blackjetrock/pico-rom-emulator/code/pico-rom-em/scope_traces/rl_ram_siz1.jpg

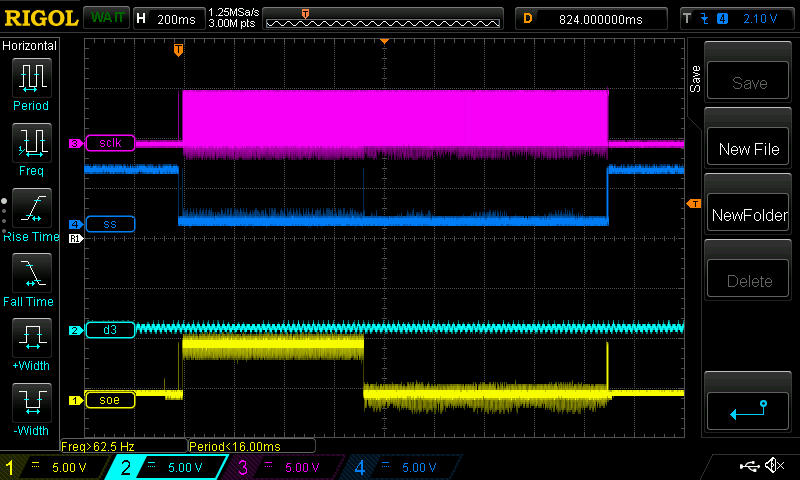
code/pico-rom-em/scope_traces/rl_ram_siz1.jpg
