blackjetrock/pico-rom-emulator/code/pico-rom-em/scope_traces/isr1.jpg

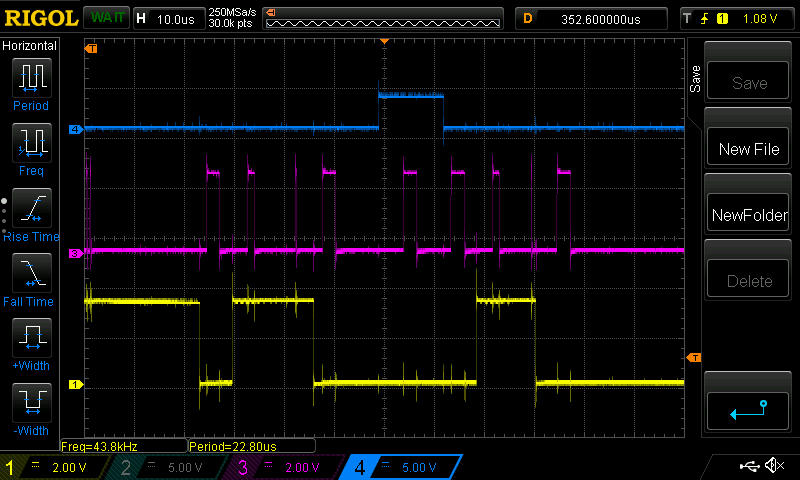
code/pico-rom-em/scope_traces/isr1.jpg
