blackjetrock/pico-rom-emulator/code/pico-rom-em/scope_traces/NewFile1.jpg

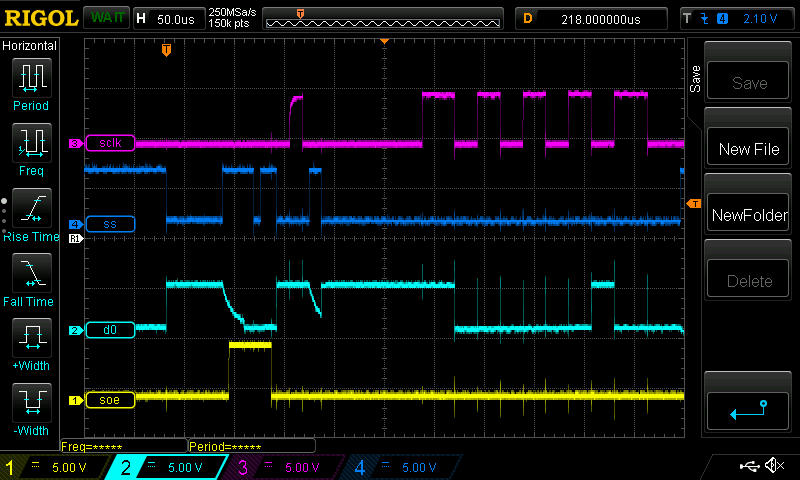
code/pico-rom-em/scope_traces/NewFile1.jpg
