blackjetrock/pico-rom-emulator/code/pico-rom-em/scope_traces/NewFile3.jpg

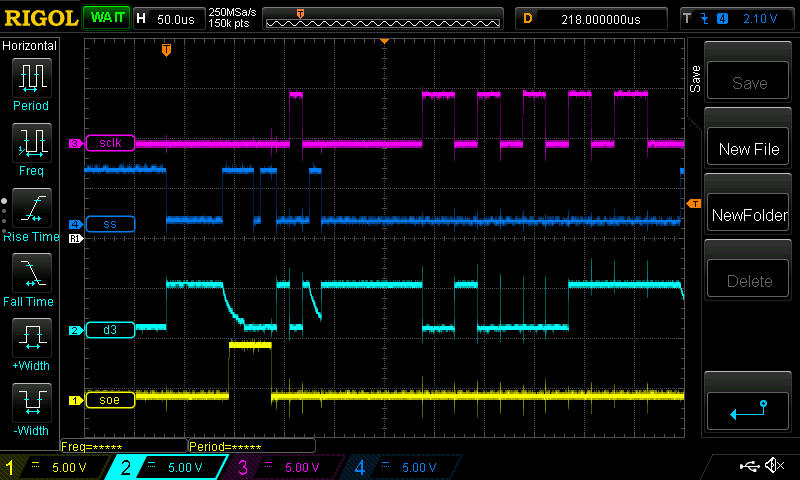
code/pico-rom-em/scope_traces/NewFile3.jpg
