blackjetrock/pico-rom-emulator/code/pico-rom-em/scope_traces/NewFile4.jpg

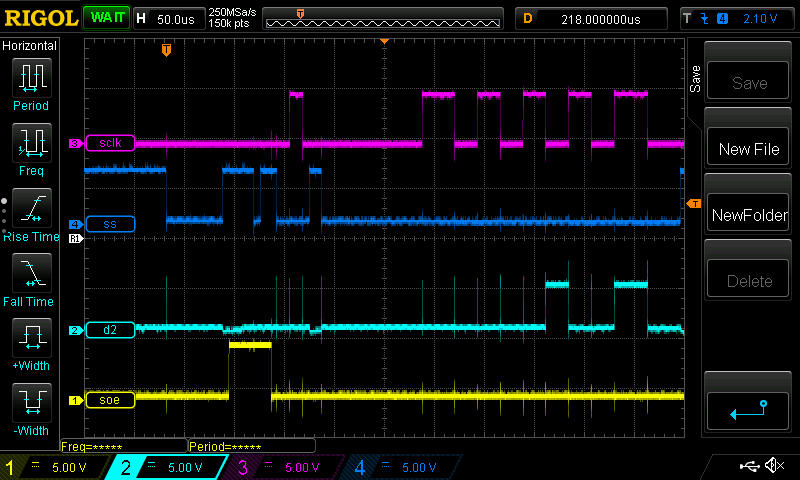
code/pico-rom-em/scope_traces/NewFile4.jpg
