blackjetrock/pico-rom-emulator/code/pico-rom-em/scope_traces/NewFile5.jpg

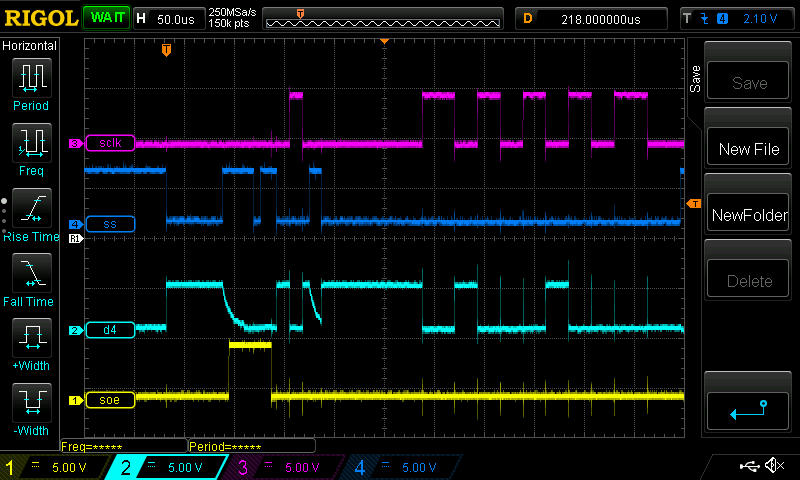
code/pico-rom-em/scope_traces/NewFile5.jpg
