blackjetrock/pico-rom-emulator/code/pico-rom-em/scope_traces/NewFile7.jpg

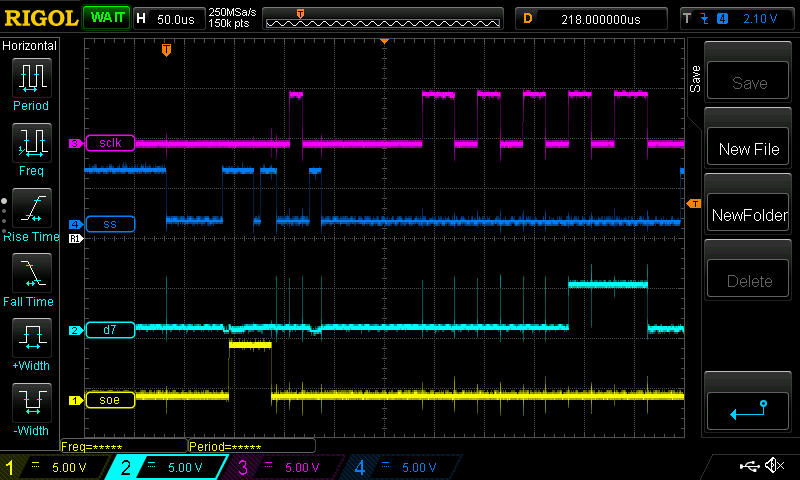
code/pico-rom-em/scope_traces/NewFile7.jpg
