blackjetrock/pico-rom-emulator/code/pico-rom-em/scope_traces/NewFile8.jpg

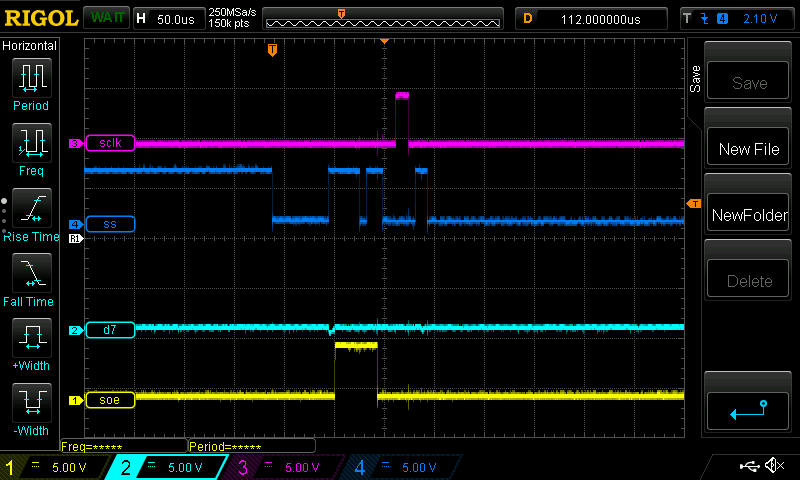
code/pico-rom-em/scope_traces/NewFile8.jpg
