blackjetrock/pico-rom-emulator/code/pico-rom-em/scope_traces/NewFile9.jpg

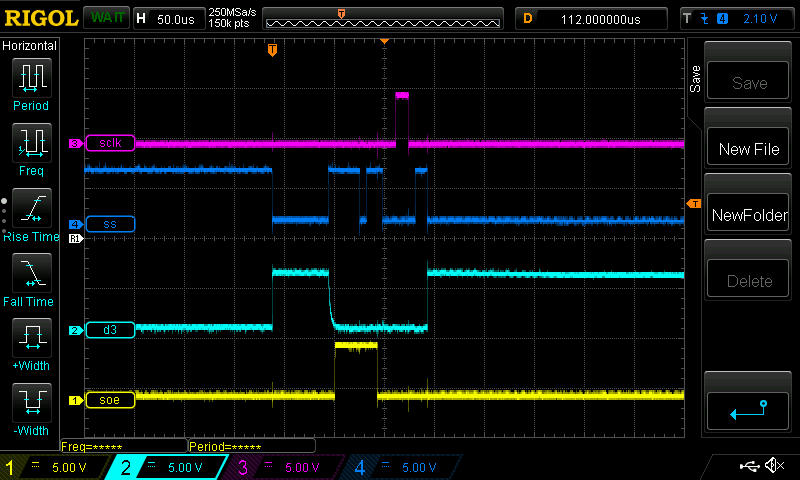
code/pico-rom-em/scope_traces/NewFile9.jpg
