blackjetrock/pico-rom-emulator/code/pico-rom-em/scope_traces/on1.jpg

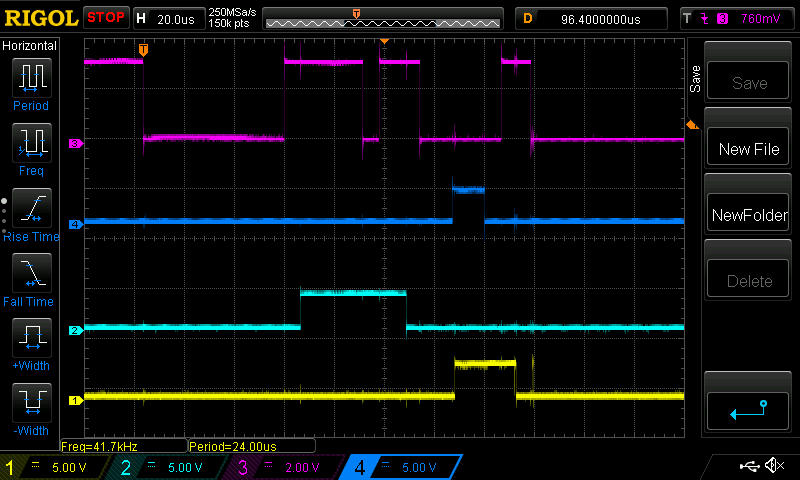
code/pico-rom-em/scope_traces/on1.jpg
