blackjetrock/pico-rom-emulator/code/pico-rom-em/scope_traces/on1b.jpg

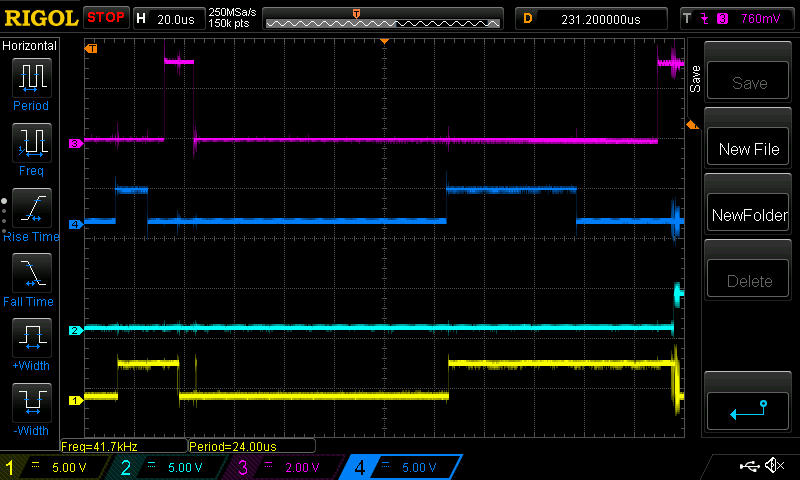
code/pico-rom-em/scope_traces/on1b.jpg
