blackjetrock/pico-rom-emulator/code/pico-rom-em/scope_traces/on2.jpg

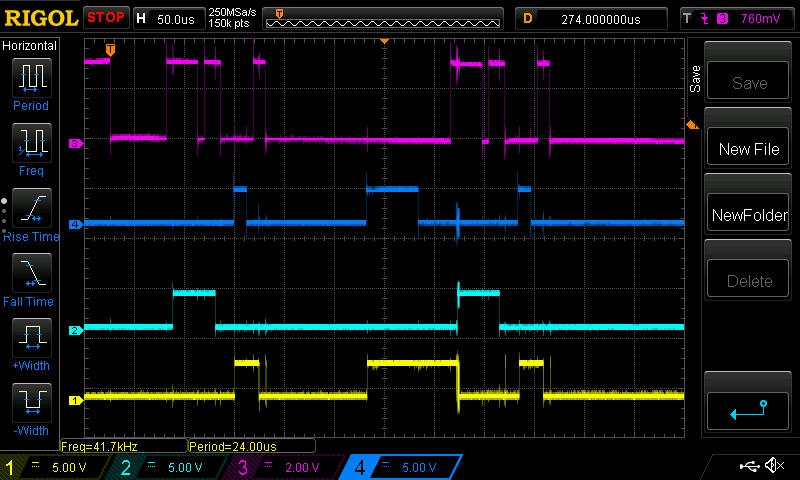
code/pico-rom-em/scope_traces/on2.jpg
