blackjetrock/pico-rom-emulator/code/pico-rom-em/scope_traces/RAMPAK1.jpg

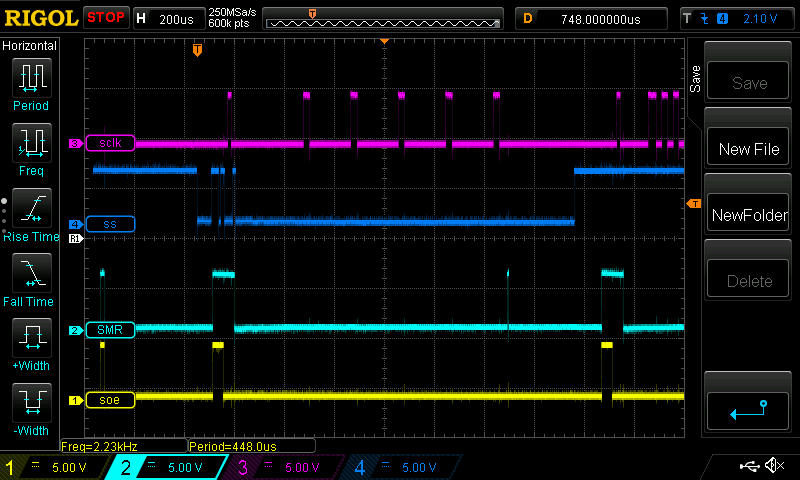
code/pico-rom-em/scope_traces/RAMPAK1.jpg
