blackjetrock/pico-rom-emulator/code/pico-rom-em/scope_traces/RAMPAK3.jpg

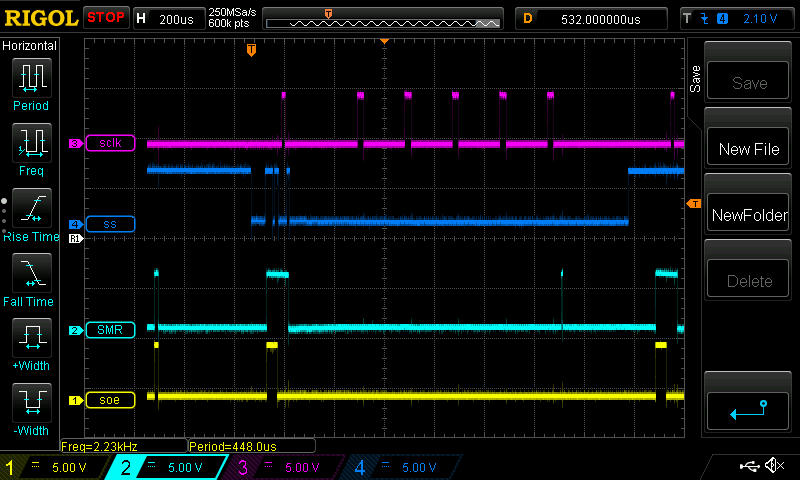
code/pico-rom-em/scope_traces/RAMPAK3.jpg
