blackjetrock/pico-rom-emulator/code/pico-rom-em/scope_traces/RDONLY1.jpg

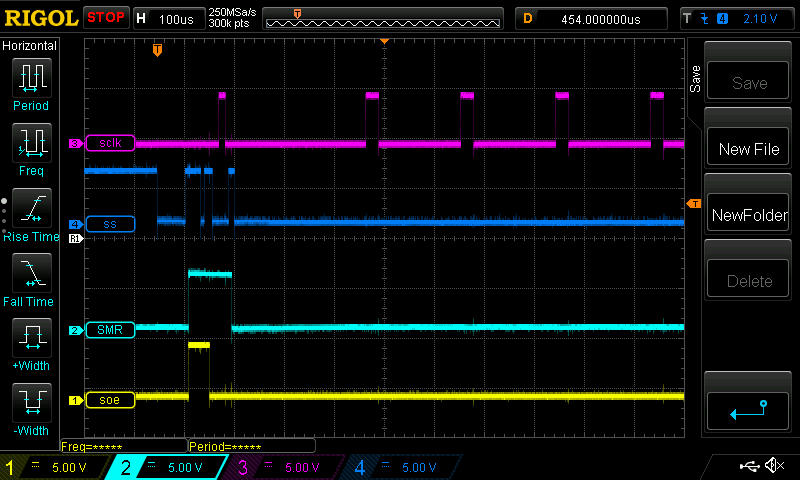
code/pico-rom-em/scope_traces/RDONLY1.jpg
