blackjetrock/pico-rom-emulator/code/pico-rom-em/scope_traces/rl_ep_pgm.jpg

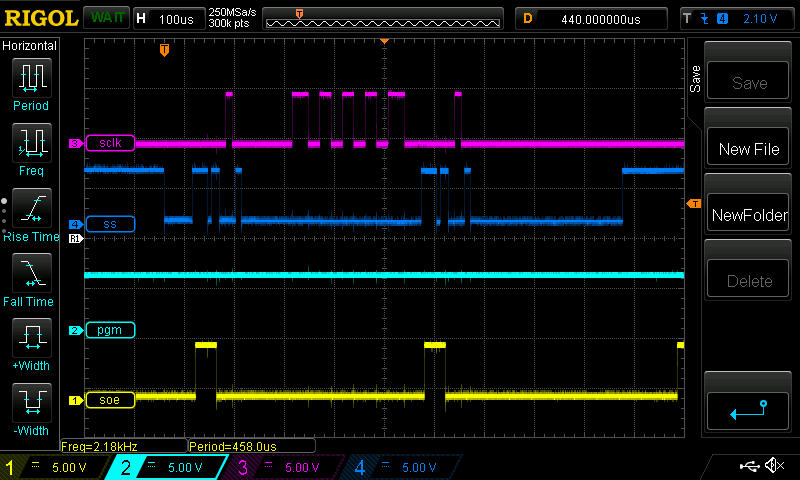
code/pico-rom-em/scope_traces/rl_ep_pgm.jpg
