blackjetrock/pico-rom-emulator/code/pico-rom-em/scope_traces/rl_epd1.jpg

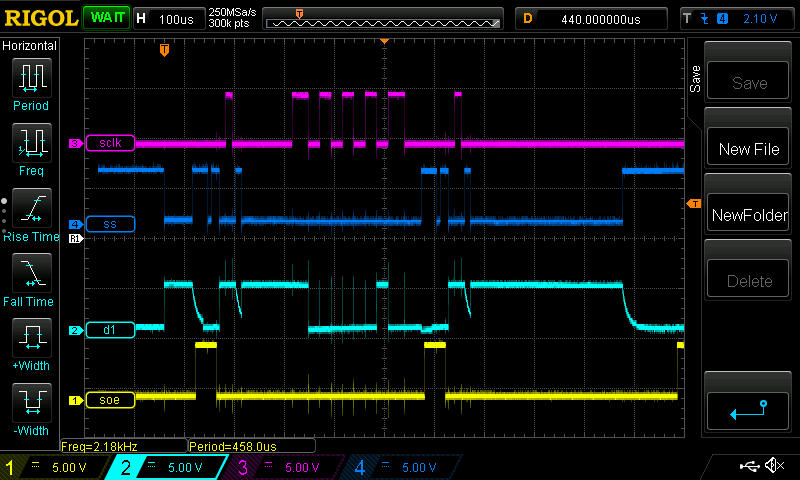
code/pico-rom-em/scope_traces/rl_epd1.jpg
