blackjetrock/pico-rom-emulator/code/pico-rom-em/scope_traces/rl_ra_smr.jpg

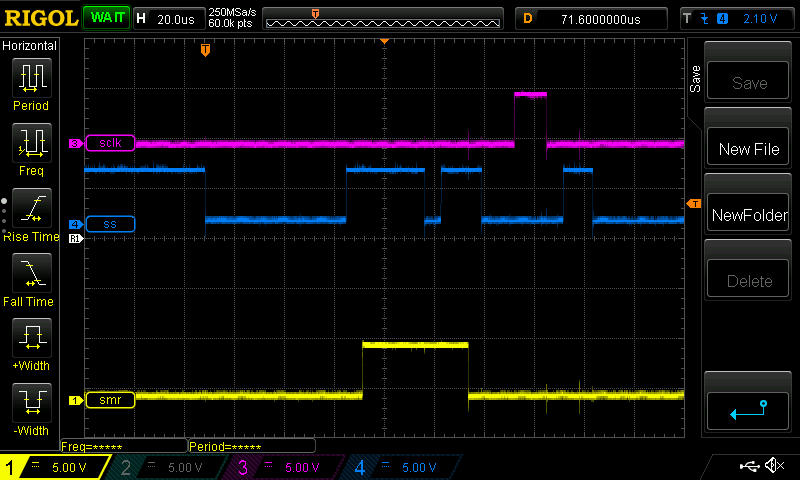
code/pico-rom-em/scope_traces/rl_ra_smr.jpg
