blackjetrock/pico-rom-emulator/code/pico-rom-em/scope_traces/rra1.jpg

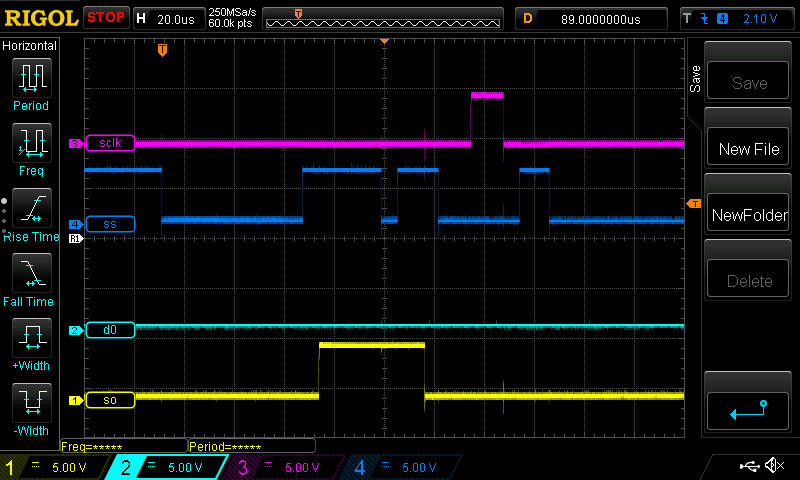
code/pico-rom-em/scope_traces/rra1.jpg
