blackjetrock/pico-rom-emulator/code/pico-rom-em/scope_traces/rra3.jpg

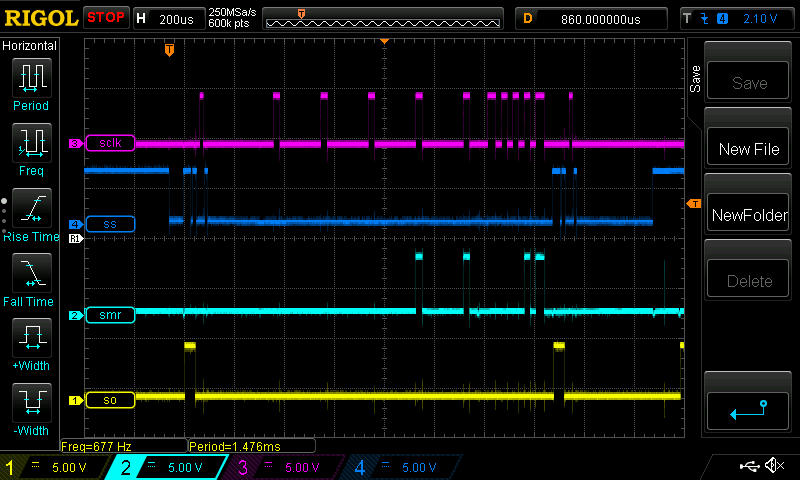
code/pico-rom-em/scope_traces/rra3.jpg
