blackjetrock/pico-rom-emulator/code/pico-rom-em/pico-rom-em.c

////////////////////////////////////////////////////////////////////////////////
//
// Pico ROM Emulator
//
////////////////////////////////////////////////////////////////////////////////


#include <ctype.h>
#include <stdio.h>
#include <string.h>
#include <stdlib.h>
#include "pico/stdlib.h"
//#include "hardware/i2c.h"
#include "hardware/pio.h"
#include "hardware/clocks.h"
#include "pico/multicore.h"

#include "f_util.h"

#include "ff.h"
#include "ff_stdio.h"
#include "hw_config.h"
#include "my_debug.h"
#include "rtc.h"
#include "sd_card.h"

// Use this if breakpoints don't work
#define DEBUG_STOP {volatile int x = 1; while(x) {} }

//-----------------------------------------------------------------------------
//
// ROM Emulator Flags

// OE pin used to switch data direction
// If 0 then DDIR_A15 used, under processor conrol

#define USE_OE_FOR_DATA_DIRECTION 1

// The address lines we are looking at

// Do we run emulation on second core?
#define EMULATE_ON_CORE1   1

#define ROM_SIZE  32*1024
#define ADDRESS_MASK (ROM_SIZE - 1)

// Map from memory space to ROM address space
#define MAP_ROM(X) (X & ADDRESS_MASK)

uint8_t rom_data[ROM_SIZE] =
  {
   // ASSEMBLER_EMBEDDED_CODE_START
0x72,0x40,0x14,0x71,0xe0,0x14,0x8e,0x00,0xff,0xbd,0xab,0x07,0x4f,0x97,0x01,0xbd,
0xd8,0x4b,0x96,0x14,0x2b,0x60,0xce,0x04,0x00,0xcc,0x55,0xaa,0xed,0x00,0xa3,0x00,
0x26,0x08,0x08,0x8c,0x7f,0xff,0x26,0xf1,0x20,0x54,0x08,0x8c,0x40,0x00,0x27,0x4e,
0x8c,0x60,0x00,0x27,0x49,0xbd,0xa5,0x7f,0x20,0x37,0x07,0xd6,0x08,0xfd,0x20,0x63,
0x0f,0xbd,0xab,0x38,0x8d,0x5f,0x7d,0x01,0x80,0x2b,0xfb,0xb6,0x01,0x81,0xa7,0x00,
0x08,0x5a,0x26,0xf2,0x3f,0x5b,0x7d,0x03,0x00,0xbd,0xa4,0xde,0xce,0x08,0x00,0xdf,
0x5c,0x24,0x08,0xdd,0x5c,0x18,0x93,0x5c,0xbd,0x81,0x05,0x7d,0x03,0xc0,0x71,0xbf,
0x14,0x7d,0x01,0xc0,0x20,0x8a,0xbe,0x20,0x67,0xfe,0x20,0x56,0x6e,0x00,0x72,0x80,
0x14,0xdf,0x5e,0x35,0xbd,0x81,0x16,0xbd,0xe8,0xb1,0x7d,0x03,0x80,0xbd,0x83,0xe3,
0x96,0x15,0x46,0x24,0x02,0x8d,0x62,0x7e,0xe4,0xa6,0xfc,0x20,0x63,0xd7,0x08,0x06,
0x8d,0x03,0x7e,0xab,0xdd,0xcc,0x40,0x40,0xbd,0xab,0x1e,0xce,0x22,0x88,0x39,0xbd,
0x81,0x9a,0xde,0x5c,0x3c,0x7b,0x02,0x15,0x27,0x17,0xcc,0x08,0x00,0x8d,0x46,0xbd,
0x81,0xaa,0x38,0xbd,0x81,0xb9,0x8d,0xd2,0xde,0x5c,0x8c,0x08,0x00,0x27,0x2d,0x20,
0x07,0x38,0x09,0xbd,0x81,0xad,0x8d,0xc2,0xbd,0xab,0xd7,0x7c,0x23,0x4a,0xfe,0x20,
0xcd,0x8c,0x00,0x0f,0x24,0x03,0xce,0x00,0x0f,0xff,0x20,0xcd,0xdf,0x7d,0x96,0x15,
0x46,0x25,0x06,0xbd,0x8a,0x76,0x3f,0x47,0x39,0xbd,0x8a,0x5f,0xbf,0x20,0x67,0xfe,
0x20,0x58,0x6e,0x00,0x4f,0x04,0x18,0x24,0x0a,0x08,0x20,0x03,0x7d,0x03,0x40,0x7d,
0x03,0x40,0x09,0x26,0xf7,0x39,0xdc,0x5e,0x4a,0xfd,0x20,0x65,0xdd,0xa5,0x86,0x7e,
0x97,0x40,0xce,0x00,0x0a,0xdf,0x6b,0xce,0x00,0x04,0xdf,0x69,0xce,0x23,0xeb,0xff,
0x24,0x03,0xc6,0x18,0x8d,0x56,0x4f,0x5f,0x97,0x63,0xdd,0x6d,0x97,0xa4,0xb7,0x20,
0xc4,0x5a,0xf7,0x20,0xc1,0xdd,0x97,0xd7,0x8b,0xf7,0x23,0xd4,0x86,0x20,0xb7,0x20,
0xc2,0x4c,0xb7,0x20,0xc3,0xce,0x82,0x9b,0xc6,0x1e,0xd7,0x42,0xcc,0x20,0x42,0xbd,
0x87,0x06,0xce,0x82,0xb9,0xff,0x23,0xe7,0x86,0x05,0xb7,0x23,0xe6,0x7f,0x23,0xe9,
0xbd,0xab,0x27,0xbd,0xa1,0x66,0xcc,0x04,0x00,0xfd,0x23,0x2b,0xfd,0x23,0x29,0xbd,
0xa6,0x10,0xce,0x20,0xd7,0xc6,0x00,0xf7,0x21,0x86,0xc6,0xaf,0x7e,0x87,0xb8,0x7d,
0x03,0x00,0x7d,0x03,0xc0,0x39,0x7d,0x03,0x80,0x39,0x7f,0x20,0x62,0x8d,0xf7,0x72,
0x01,0x5b,0x7d,0x00,0x5b,0x26,0xfb,0x39,0x8d,0xf0,0xce,0x07,0xff,0x7d,0x03,0x40,
0x09,0x7b,0x02,0x15,0x27,0xf7,0x08,0x27,0xee,0xcc,0x00,0x3c,0xbd,0x86,0xb1,0xce,
0x20,0xc5,0x7e,0xe8,0xcb,0x4f,0x97,0x5b,0x7d,0x20,0x62,0x26,0x05,0x4c,0xb7,0x20,
0x62,0x3b,0xf6,0x20,0xc9,0x37,0xc6,0x01,0x8d,0xe5,0x33,0xf1,0x20,0xc9,0x27,0x08,
0x7d,0x23,0x35,0x27,0x03,0x7c,0x23,0x4a,0x96,0x7c,0x27,0x07,0xde,0x7d,0x27,0x03,
0x09,0xdf,0x7d,0x3b,0xbd,0xd8,0x4b,0xbd,0x88,0xb4,0x54,0x52,0x41,0x50,0x00,0x1a,
0x20,0xfd,0x36,0x07,0x0f,0xb7,0x20,0x6f,0x32,0xfd,0x20,0x69,0xff,0x20,0x6b,0x38,
0xa6,0x00,0x2b,0x19,0xff,0x20,0x6d,0xce,0x00,0x0e,0x48,0x2a,0x06,0xe6,0x4c,0x37,
0xe6,0x4b,0x37,0x09,0x09,0x26,0xf3,0xfe,0x20,0x6d,0x08,0x20,0x2e,0xce,0x00,0x4d,
0x44,0x24,0x06,0x33,0xe7,0x00,0x33,0xe7,0x01,0x08,0x08,0x8c,0x00,0x5b,0x26,0xf0,
0x20,0x1a,0x32,0xb7,0x20,0x6f,0x33,0x32,0xfd,0x20,0x69,0x38,0xff,0x20,0x6b,0x38,
0xe6,0x00,0x08,0x3c,0xfe,0x23,0xe7,0x3a,0x3a,0xee,0x00,0x3c,0xfe,0x20,0x6b,0xfc,
0x20,0x69,0x36,0xb6,0x20,0x6f,0x06,0x32,0x39,0xfe,0x20,0x42,0x6e,0x00,0xfe,0x20,
0x44,0x6e,0x00,0xfe,0x20,0x46,0x6e,0x00,0xfe,0x20,0x48,0x6e,0x00,0xfe,0x20,0x4a,
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

// ASSEMBLER_EMBEDDED_CODE_END
  };

//------------------------------------------------------------------------------

const int D0_PIN = 0;
const int D1_PIN = 1;
const int D2_PIN = 2;
const int D3_PIN = 3;
const int D4_PIN = 4;
const int D5_PIN = 5;
const int D6_PIN = 6;
const int D7_PIN = 7;

//
// The address lines (always inputs)
//
const int  A0_PIN  =  8;
const int  A1_PIN  =  9;
const int  A2_PIN  = 10;
const int  A3_PIN  = 11;
const int  A4_PIN  = 12;
const int  A5_PIN  = 13;
const int  A6_PIN  = 14;
const int  A7_PIN  = 15;
const int  A8_PIN  = 16;
const int  A9_PIN  = 17;
const int  A10_PIN = 18;
const int  A11_PIN = 19;
const int  A12_PIN = 20;
const int  A13_PIN = 21;
const int  A14_PIN = 22;
const int  DDIR_A15_PIN = 26;

const int OE_PIN = 27;
const int CE_PIN = 28;

// Arrays for setting GPIOs up
#define NUM_ADDR 16
#define NUM_DATA 8

const int address_pins[NUM_ADDR] =
  {
   A0_PIN,
   A1_PIN,
   A2_PIN,
   A3_PIN,
   A4_PIN,
   A5_PIN,
   A6_PIN,
   A7_PIN,
   A8_PIN,
   A9_PIN,
   A10_PIN,
   A11_PIN,
   A12_PIN,
   A13_PIN,
   A14_PIN,
   DDIR_A15_PIN,
  };

const int data_pins[NUM_DATA] =
  {
   D0_PIN,
   D1_PIN,
   D2_PIN,
   D3_PIN,
   D4_PIN,
   D5_PIN,
   D6_PIN,
   D7_PIN,
  };

////////////////////////////////////////////////////////////////////////////////

//-----------------------------------------------------------------------------
//
// Put a value on the data bus

inline void set_data(BYTE data)
{
  int states;
  int dat = data & 0xff;
  
  // Direct register access to make things faster
  sio_hw->gpio_set = (  dat  << 0);
  sio_hw->gpio_clr = ((dat ^ 0xFF) << 0);
}



////////////////////////////////////////////////////////////////////////////////
//
// Set things up then sit in a loop waiting for the emulated devcie to
// be selected
//
////////////////////////////////////////////////////////////////////////////////

#define MAX_ADDR_TRACE 1024*64
int trace_on = 0;
volatile int addr_trace_index = 0;
volatile uint16_t addr_trace[MAX_ADDR_TRACE];
volatile unsigned int number_ce_assert = 0;

void rom_emulate(void)
{
  while(1)
    {
      uint32_t gpio_states;
      BYTE db;
      unsigned int addr;
      
      //      gpio_put(DDIR_A15_PIN, 1);
      
      // read GPIOs
      gpio_states = sio_hw->gpio_in;
      
      
      // We look for CE
      //      if( gpio_states & (1 << CE_PIN) )
      //	{
      // CE high, we are not selected
      //	}
      //else
      //	{
      
      
      // CE low, we are selected
      // ROM emulation so always a read of us
      // get address
      addr = (gpio_states >> 8) & ADDRESS_MASK;
	  
      // Get data and present it on bus
      set_data(rom_data[addr]);
	  
      //set_data(0xF8);
	  
      // Trace address
      if( addr == 0x0097 )
	{
	  trace_on = 1;
	}
	  
      if( trace_on)
	{
	  if( addr_trace_index < MAX_ADDR_TRACE )
	    {
	      int tv = addr;
	      if( addr_trace[addr_trace_index] == tv )
		{
		}
	      else
		{
		  addr_trace_index++;
		  addr_trace[addr_trace_index] = tv;
		}
	      //addr_trace_index %= MAX_ADDR_TRACE;
		  
	    }
	}
      number_ce_assert++;
#if 0
      // Wait for CE to be de-asserted
      while(1)
	{
	  gpio_states = sio_hw->gpio_in;
	      
	  // We look for CE
	  if( gpio_states & (1 << CE_PIN) )
	    {
	      // CE high, we are not selected
	      break;
	    }
	      
	}
#endif
    }
}


int main()
{



#if 0
  // Set up test program
  rom_data[MAP_ROM(0xFFFC)] = 0x00;
  rom_data[MAP_ROM(0xFFFD)] = 0xF8;
  rom_data[MAP_ROM(0xFFFE)] = 0x00;
  rom_data[MAP_ROM(0xFFFF)] = 0xF8;

  rom_data[MAP_ROM(0xF800)] = 0xE8;
  rom_data[MAP_ROM(0xF801)] = 0x4C;
  rom_data[MAP_ROM(0xF802)] = 0x00;
  rom_data[MAP_ROM(0xF803)] = 0xF8;
#endif

#if 0
  for(int i=0; i< 2048; i+=4)
    {
      rom_data[MAP_ROM(i+0)] = 0xEB;
      rom_data[MAP_ROM(i+1)] = 0x4C;
      rom_data[MAP_ROM(i+2)] = 0x00;
      rom_data[MAP_ROM(i+3)] = 0xF8;
    }

  rom_data[MAP_ROM(0xFFFC)] = 0x00;
  rom_data[MAP_ROM(0xFFFD)] = 0xF8;
  rom_data[MAP_ROM(0xFFFE)] = 0x00;
  rom_data[MAP_ROM(0xFFFF)] = 0xF8;
#endif

#if 0
    for(int i=0; i< 2048; i+=4)
    {
      rom_data[i] = 0x4c;
    }
#endif
    
  //DEBUG_STOP;
  
  char line[80];

  stdio_init_all();

  printf("\nPico ROM Emulator\n");
  
#if TEST_STDIO
  {
  int count;
  while (true)
    {
      count++;
      
      if( (count % 1000000) == 0 )
	{
	  sprintf(line, "\nRP2040: %d", count);
	  printf(line);
	}
    }
  }
#endif

  printf("\nSetting GPIOs...");

  for (int i=0; i<NUM_ADDR; i++)
    {
      // Set up directions for the control lines
      gpio_init(address_pins[i]);
      gpio_set_dir(address_pins[i], GPIO_IN);
    }

  for (int i=0; i<NUM_DATA; i++)
    {
      // Set up directions for the control lines
      gpio_init(data_pins[i]);
      gpio_set_dir(data_pins[i], GPIO_OUT);
    }

  gpio_init(OE_PIN);
  gpio_set_dir(OE_PIN, GPIO_IN);
  gpio_init(CE_PIN);
  gpio_set_dir(CE_PIN, GPIO_IN);

  // DEBUG: Use DDIR_A15 as status line
  gpio_init(DDIR_A15_PIN);
  gpio_set_dir(DDIR_A15_PIN, GPIO_OUT);

  int ce = 0;

#if 0
  while(1)
    {
      ce = gpio_get(CE_PIN);
      gpio_put(DDIR_A15_PIN, ce);
    }
#endif

#if 0
  while(1)
    {
      uint32_t gpio_states;
      gpio_states = sio_hw->gpio_in;
      if( gpio_states & (1 << CE_PIN))
	{
	  gpio_put(DDIR_A15_PIN, 1);
	}
      else
	{
	  gpio_put(DDIR_A15_PIN, 0);
	}
    }
#endif

  
  //set_data_outputs();
#if 0
#if !USE_OE_FOR_DATA_DIRECTION


  // LS_DIR is an output
  gpio_set_dir(LS_DIR_PIN, GPIO_OUT);
#else
  gpio_put(DDIR_A15_PIN, 0);
  gpio_set_dir(DDIR_A15_PIN, GPIO_OUT);
#endif
#endif
  

  // Use a polling loop for minimum latency
#if 0
  // Turn off timer interrupts
  irq_set_mask_enabled(0xf, false);
#endif
  
  // We set the CE of the level shifters to be driven by OE on the
  // host board, and the direction (A->B) to be set up by the Pico
  // The data direction can be left as output from the Pico as
  // the OE/CE line will drive on to the data bus when OE is asserted


#if 0
  while(1)
    {
      set_data(0xf8);
    }
#endif

#if EMULATE_ON_CORE1
  multicore_launch_core1(rom_emulate);
  while(1)
  {
	    }


#else
  rom_emulate();
#endif
  
      //      gpio_put(DDIR_A15_PIN, 0);

}
